A-Letourneau/Projet_Final_TSO/Documentation/Osentreprendre/presentation_mallette_devasion_Louis_Alexis.pdf

# Malette d’évasion

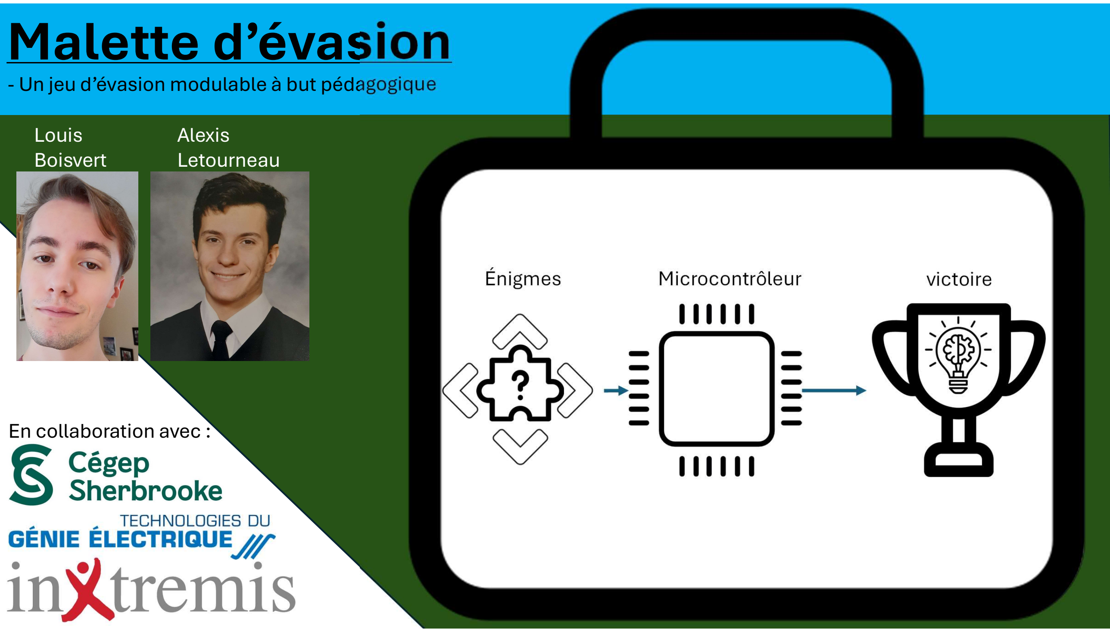
[picture p85: page 1]

Énigmes | Microcontrôleur

Louis
Boisvert

Alexis
Letourneau

victoire

- Un jeu d’évasion modulable à but pédagogique

En collaboration avec :
