A-Letourneau/Projet_Final_TSO/Code/Mallette_GUI/Proto_Fonct_PI/trophy.png

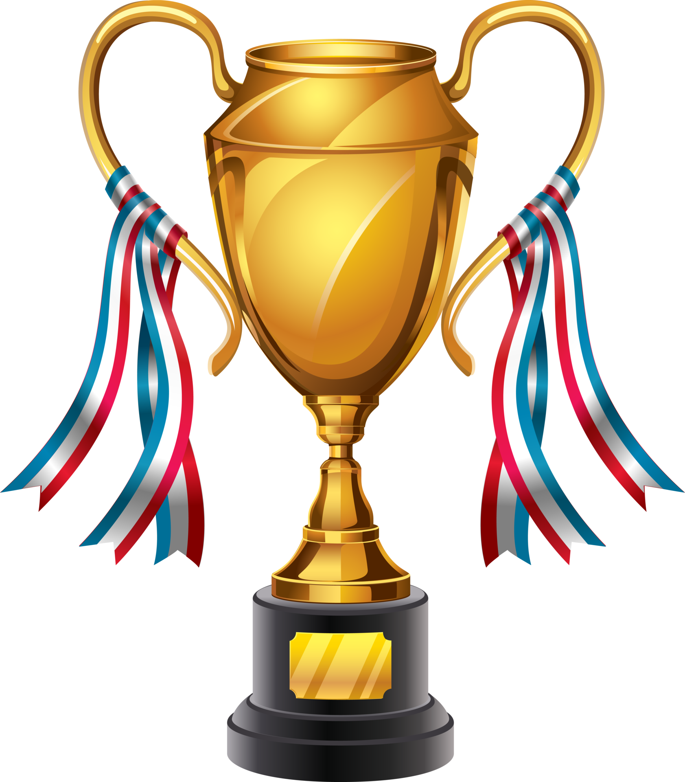
Code/Mallette_GUI/Proto_Fonct_PI/trophy.png
