A-Letourneau/Projet_Final_TSO/Documentation/Manuel_Technique/mallette PIC/20250507_090922.jpg

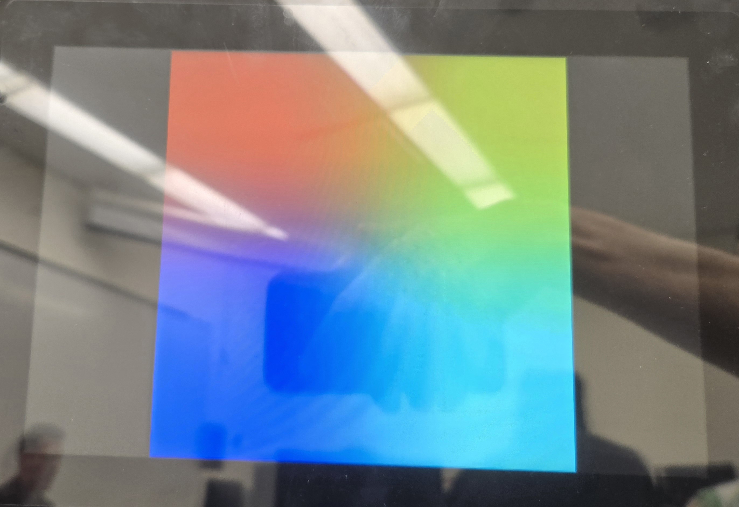
Documentation/Manuel_Technique/mallette PIC/20250507_090922.jpg
