A-Letourneau/Projet_Final_TSO/Documentation/Manuel_Technique/mallette PIC/20250507_091233.jpg

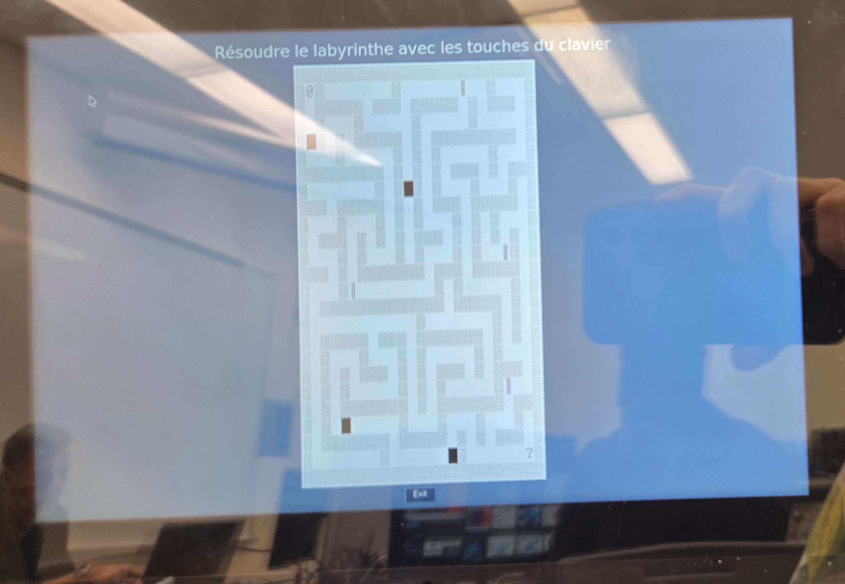
Documentation/Manuel_Technique/mallette PIC/20250507_091233.jpg
