A-Letourneau/Projet_Final_TSO/Documentation/Manuel_Technique/mallette PIC/20250507_091244.jpg

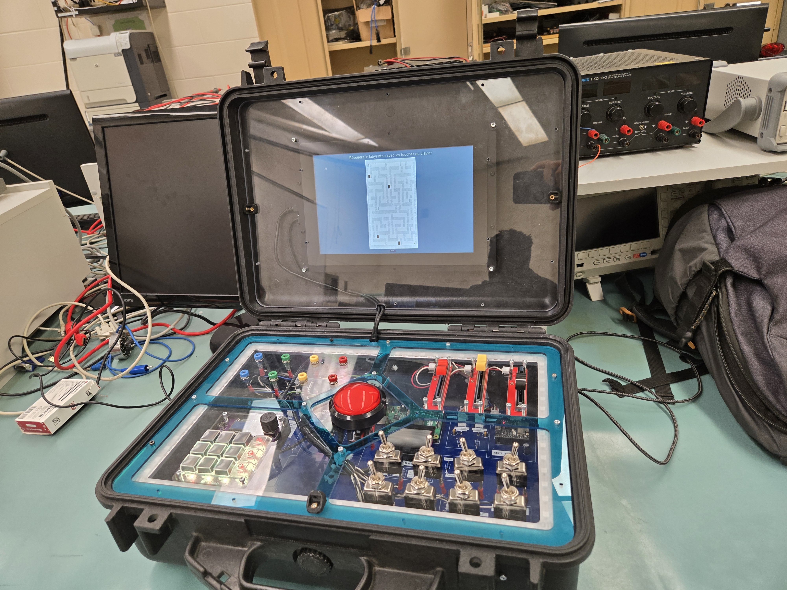
Documentation/Manuel_Technique/mallette PIC/20250507_091244.jpg
