A-Letourneau/Projet_Final_TSO/Matériel/PCB mallette Altium/Raspberry_Pi_4_ModelB.pdf

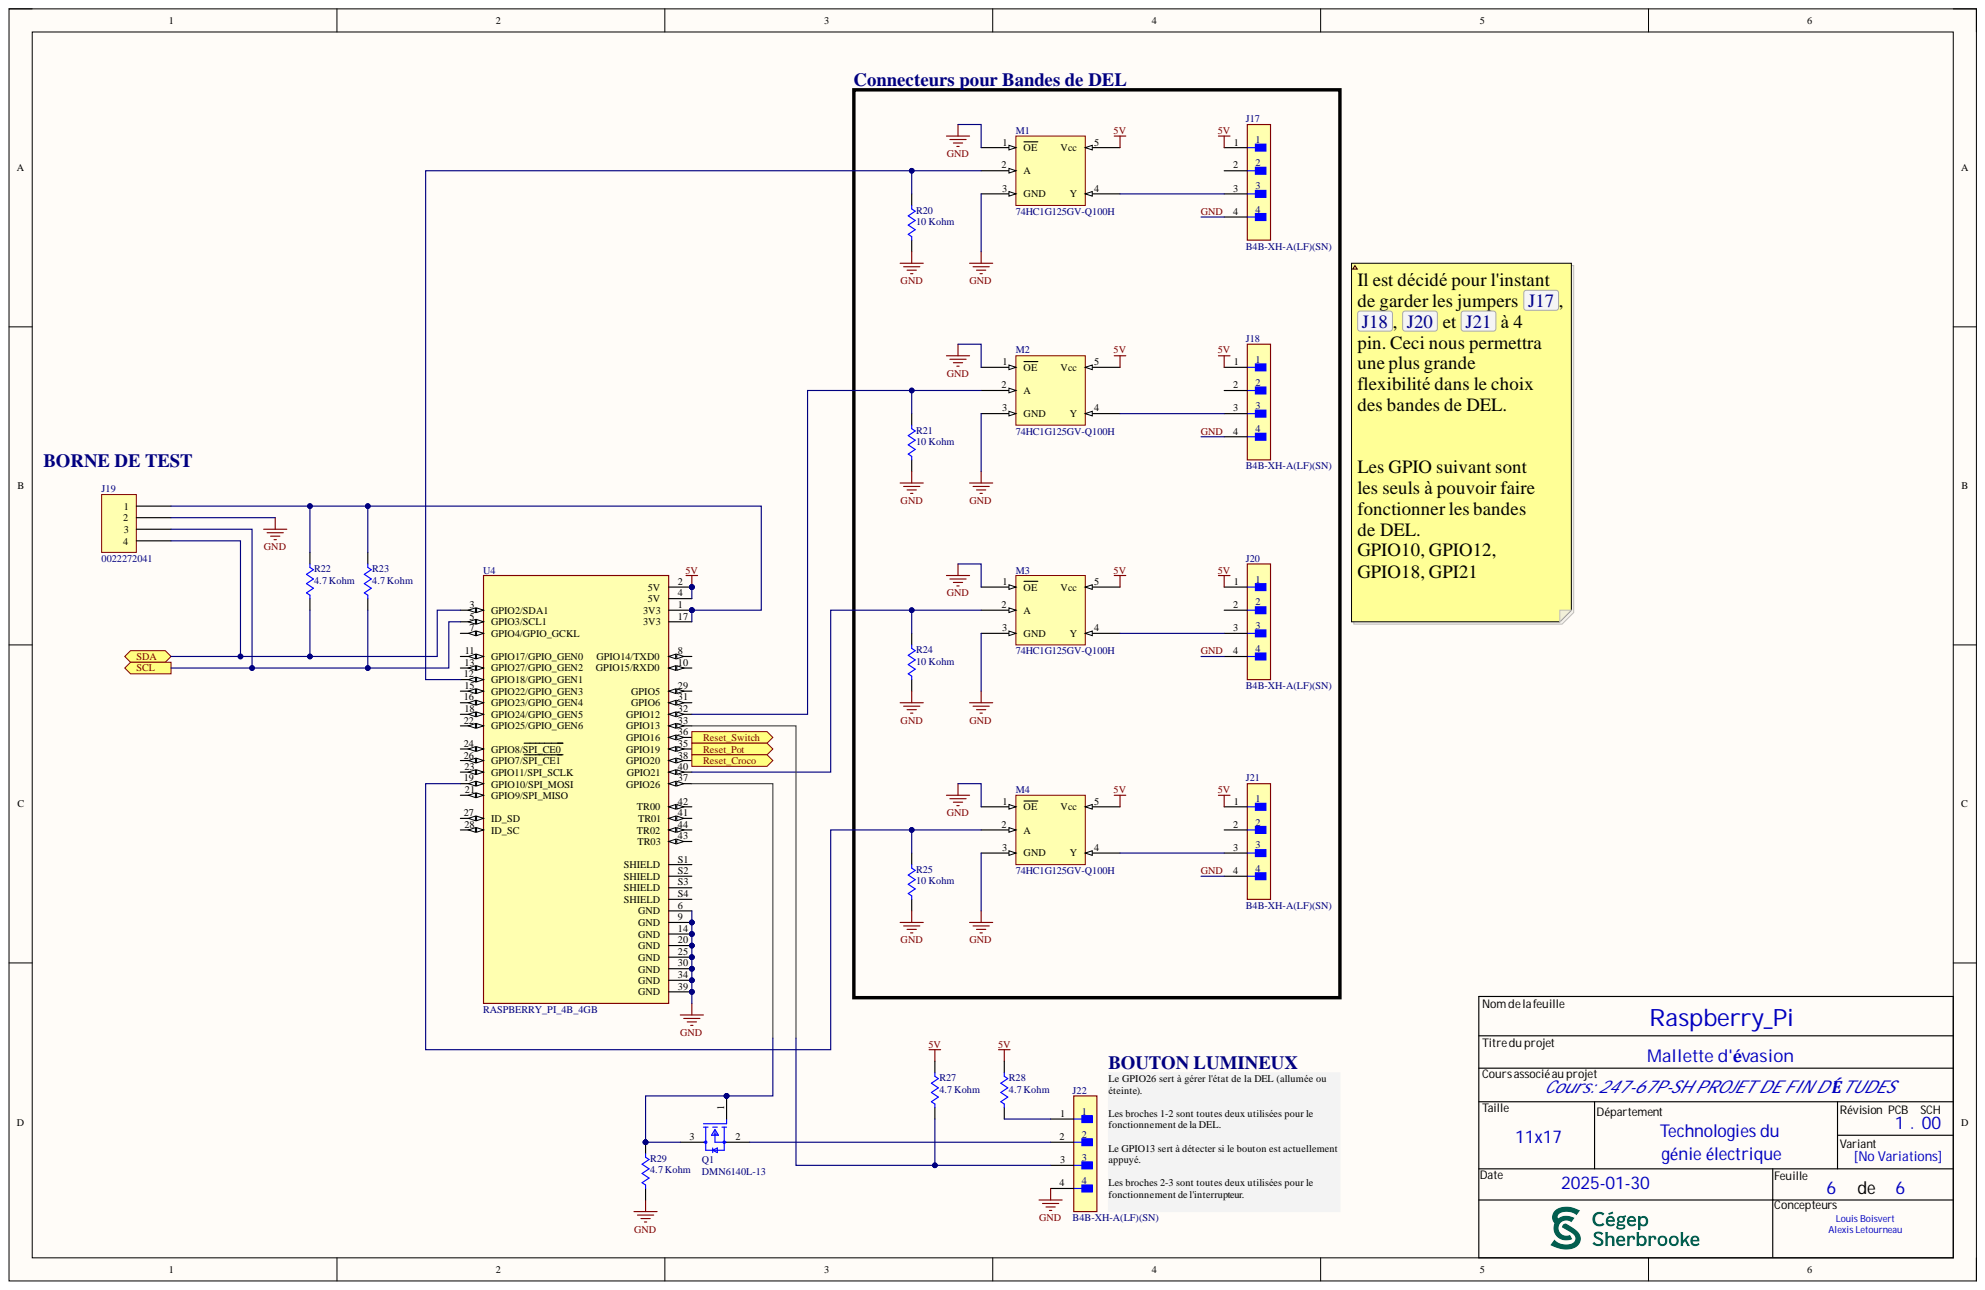
[picture p156: page 1]

Connecteurs pour Bandes de DEL

Il est décidé pour l'instant
de garder les jumpers J17 ,
pin. Ceci nous permettra
une plus grande
flexibilité dans le choix
des bandes de DEL.

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

Nom de la feuille

Titredu projet
Mallette d'évasion Cours associé au projet

Le GPIO26 sert à gérer l'état de la DEL (allumée ou
éteinte).

Cours: 247-67P-SH PROJET DE FIN D'ÉTUDES

Les broches 1-2 sont toutes deux utilisées pour le
fonctionnement de la DEL.

Le GPIO13 sert à détecter si le bouton est actuellement
appuyé.

Les broches 2-3 sont toutes deux utilisées pour le
fonctionnement de l'interrupteur.
