A-Letourneau/Projet_Final_TSO/Code/Mallette_GUI/Proto_Fonct_PI/main.py

#!/home/beaulibe/monenv/bin/python3
"""
Auteur : Alexis Létourneau
Date : 2024-12-03
Environnement : Python, Thonny, raspberry pi 4, ESP32-C3-WROOM-02 Devkit, 
Brief : Programme qui affiche les données reçu par la communication i2c de 3 esp32 externes en mode Sub et qui affiche leurs donnees avec interface PySimpleGUI.
Ce programme communique en i2c en mode Main avec les 3 esp32 en mode Sub. 
Les 3 esp32 ont des objets interactifs (potentiomètres, boutons, interrupteurs) différents, 
Celui nommé SW contient quatre boutons
Celui nommé POT contient 3 potentiomètres et 2 interrupteurs.
Celui nomme Croco est 8 entrees qui transmet si deux des entrees sont interconnecte.
Les lectures de ces objets sont transmises par JSON à la demande du Main à toutes les 50ms


Les 3 esp32 ont une interface chaque, qui contient des "widget" qui représentent leurs états.
L'interface POT utilise deux images d'interrupteurs pointant vers la gauche ou la droite fait en base64, ce qui permet d'avoir le fichier de l'image dans le fichier py directement. 
et utilise des "ProgressBar" pour montrer l'état des potentiomètres.
L'interface SW utilise des images d'interrupteurs pour démontrer l'état des interrupteurs.
L'interface Croco utilise des cercles de couleurs pour montrer qu'elle entrees du esp32 est interconnectee.
Quand on ferme une des fenêtres, les deux se ferme.

"""
#importation des library standard
from smbus2 import SMBus, i2c_msg   #Pour la communication i2c
import PySimpleGUI as sg            #Pour l'interface graphique
import board
from digitalio import DigitalInOut, Direction, Pull
import time
from rpi_ws281x import PixelStrip, Color

#importation des library créer
import moduleDEL    #import Del library obsolète, car elle cause des erreurs lorsqu'il y a plusieurs bandes de dels adressables
from Class_Croco import Croco
import I2c_Comm
from Class_SW import SW_MODULE
from Class_POT import POT
from mazeModule import mazeClass
from button import BTN_CLASS

#Les deux images d'interrupteurs en base 64
TOGGLE_SW_OFF = b'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'
TOGGLE_SW_ON = b'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'

#Les addresses des Sub
SLAVE_ADDRESS_Croco = 0x0b
SLAVE_ADDRESS_SW = 0x0a
SLAVE_ADDRESS_POT = 0x09

#La valeur de refresh en ms
REFRESH_RATE = 50

#Pour les print
DEBUG = False
DEL_ACTIVE = True

# The number of NeoPixels
num_pixels = 100

# luminosités des bandes de dels
lumin = 50

# Pin number
pinStrip1 = 21
#pinStrip2 = 13
pinStrip3 = 12
pinStrip4 = 18 

# Pour les equations
LIST_OPERATIVE = ["+","-","x","/"] #exemple de quatre questions possibles
# LED setup.
led = DigitalInOut(board.D26)
led.direction = Direction.OUTPUT
#BTN setup
switch = DigitalInOut(board.D13)
switch.direction = Direction.INPUT

#Reset setup
resetCroco = DigitalInOut(board.D16)
resetCroco.direction = Direction.OUTPUT

resetSwitch = DigitalInOut(board.D20)
resetSwitch.direction = Direction.OUTPUT

resetPot = DigitalInOut(board.D19)
resetPot.direction = Direction.OUTPUT


#Reset des esp32 pour init la communication
resetCroco.value = False
resetSwitch.value = False
resetPot.value = False
time.sleep(0.01)
resetCroco.value = True
resetSwitch.value = True
resetPot.value = True

def make_winSelect():
    layout_winSelect = [
            [sg.Text("Veuillez selectionner l'enigme desire", size=(35,1), key = "titleSW")],
            [sg.Button("SW"), sg.Button("POT"), sg.Button("Croco")],
            [sg.Button("Labyrinthe"), sg.Button("Bouton")],
            [sg.Button('Exit')]
         ]
    return sg.Window('Fenetre de selection', layout_winSelect, default_element_size=(12, 1) , auto_size_text=False, finalize=True) 

sg.theme("SandyBeach")
#ouvre le menu principal
window_winSelect = make_winSelect()
#window_winSelect.maximize()

#-------------------------------------fonction pour la library Del-------------------------------------#

#fait des objets pour modifier les dels.    (le num de la pin, le nombre de dels, luminosité si c'est GPIO13 ou 19)
strip1 = moduleDEL.initStrip(pinStrip1, num_pixels, lumin, False)
#strip2 = moduleDEL.initStrip(pinStrip2, num_pixels, lumin, True)
strip3 = moduleDEL.initStrip(pinStrip3, num_pixels, lumin, False)
strip4 = moduleDEL.initStrip(pinStrip4, num_pixels, lumin, False)

if DEL_ACTIVE:
    #active les objets strip pour qu'ils puissent être utilisés
    strip1.begin()
#    strip2.begin()
    strip3.begin()
    strip4.begin()


#fait des objets de classes des énigmes
my_Croco = Croco(SLAVE_ADDRESS_Croco, LIST_OPERATIVE, DEBUG, strip1)
my_SW = SW_MODULE(SLAVE_ADDRESS_SW,DEBUG)
mazeEnigme = mazeClass(mazeFile=open(f"/home/beaulibe/Desktop/Mallette_GUI/Proto_Fonct_PI/maze1.txt"), nbGate=4, SLAVE_ADDRESS_MAZE=SLAVE_ADDRESS_SW, DEBUG=DEBUG, DEL_ACTIVE=DEL_ACTIVE)
my_POT = POT(SLAVE_ADDRESS_POT,DEBUG, strip3)
buttonEnigme = BTN_CLASS(switch, led, DEBUG)


if DEL_ACTIVE:
#     moduleDEL.colorWipe(strip1, Color(255, 0, 0), 0)  # Red wipe
#     moduleDEL.colorWipe(strip2, Color(0, 255, 0), 0)  # Red wipe
#     moduleDEL.colorWipe(strip3, Color(0, 0, 255), 0)  # Red wipe
#     moduleDEL.colorWipe(strip4, Color(255, 255, 255), 0)  # Red wipe
    moduleDEL.colorInBetween(strip1, Color(255, 0, 0),0,17)  # Red wipe
    moduleDEL.colorInBetween(strip1, Color(0, 255, 0),18,35)  # Red wipe
    moduleDEL.colorInBetween(strip1, Color(0, 0, 255),36,53)  # Red wipe
    moduleDEL.colorInBetween(strip1, Color(255, 0, 255),54,71)  # Red wipe
    
    moduleDEL.rainbow(strip1,1)

#Boucle principale
while True: 

    if switch.value:
        led.value = False
        if DEBUG:
            print('BTN off')
    else:
        led.value = True
        if DEL_ACTIVE:
            moduleDEL.rainbowCycle(strip4, 0, 1)
        if DEBUG:
            print('BTN on')
        
        
    #-------------Lecture des boutons des fenetres--------------#
    window, event, value = sg.read_all_windows(timeout = REFRESH_RATE)
    
    if window == sg.WIN_CLOSED and event != sg.TIMEOUT_EVENT:
        break
    if event == 'Exit' or event == sg.WIN_CLOSED: #Si on ferme une fenetre on ferme toutes les fenetres
        window.close()
         
        if window == my_SW.window_SW:
            my_SW.window_SW = None
            
        elif window == my_POT.window_POT:
            my_POT.window_POT = None
            
        elif window == my_Croco.window_Croco:
            my_Croco.window_Croco = None
            
        elif window == mazeEnigme.window_maze:
            mazeEnigme.window_maze = None

        elif window == buttonEnigme.window:
            buttonEnigme.window = None
            
        elif window == window_winSelect:
            break
        
    # crée les interfaces utilisateurs selon le choix de l'utilisateurs 
    if event == "SW":
        if not my_SW.window_SW:
            my_SW.window_SW = my_SW.Make_WinSW()
            my_SW.window_SW.maximize()
            
    if event == "POT":
        if not my_POT.window_POT:
            my_POT.window_POT = my_POT.Make_WinPOT()
            my_POT.window_POT.maximize()
    
    if event == "Croco":
        if not my_Croco.window_Croco:
            my_Croco.window_Croco = my_Croco.Make_WinCroco()
            my_Croco.window_Croco.maximize()
            
    if event == "Bouton":
        if not buttonEnigme.window:
            buttonEnigme.window = buttonEnigme.Make_WinBTN()
#            buttonEnigme.window.maximize()        
            
    if event == "Labyrinthe":
        if not mazeEnigme.window_maze:
            mazeEnigme.startMaze()
            mazeEnigme.window_maze.maximize()
            
    #Essaye de lire les json des esp32 et met un message d'erreur s'il n'y parvient pas
    if my_Croco.window_Croco:
        my_Croco.msg_Croco = my_Croco.Croco_Json()
        my_Croco.doWinCroco()
        
    if my_SW.window_SW: 
        my_SW.msg_SW = my_SW.SW_Json()
        
    if  my_POT.window_POT:    
        my_POT.msg_POT = my_POT.POT_Json()
        my_POT.doWinPot()
    
    if mazeEnigme.window_maze:
        mazeEnigme.doMaze()
        
    if buttonEnigme.window:
        buttonEnigme.doButton()
    
    #débute les énigmes si leur fenêtre est présentement ouverte
    # et va changer les couleurs des strips de dels lorsque l'utilisateur va réussir
    

#À la fin du programme, on ferme les fenêtres s'il existe
if my_SW.window_SW:
    my_SW.window_SW.close()       
if my_POT.window_POT:    
    my_POT.window_POT.close()            
if my_Croco.window_Croco: 
    my_Croco.window_Croco.close()

print("closing")
