A-Letourneau/Projet_Final_TSO/Code/Mallette_GUI/Code de test/dinosaur.py

import PySimpleGUI as sg

"""
    Demo_Animated_GIFs.py
    
    Shows how to:
    * Use popup_animated
    * Use animated GIF in a custom window layout
    * Store your GIFs in base64 format inside this source file (copy and paste into your source file)
    
    The first image that uses popup_animated will stop after a few seconds on its own.
    The remaining images are shown 1 at a time. To move on to the next image, click the current image.
    If you want to exit before reaching the final image, right click the image and choose 'exit'
"""

# ---------------------------- Base 64 GIFs ----------------------------
gif = b'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'

# list of all of the base64 GIFs
# first show how to use popup_animated using built-in GIF image
for i in range(1000):
    sg.popup_animated(sg.DEFAULT_BASE64_LOADING_GIF, background_color='white', time_between_frames=100)
sg.popup_animated(None)      # close all Animated Popups


# Next demo is to show how to create custom windows with animations
layout = [[sg.Image(data=gif, enable_events=True, background_color='white', key='-IMAGE-', right_click_menu=['UNUSED', 'Exit'])],]

window = sg.Window('My new window', layout,
        grab_anywhere=True,
        keep_on_top=True,
        background_color='white',
        transparent_color='white',
        alpha_channel=.8,
        margins=(0,0))



while True:                                     # Event Loop
    event, values = window.read(timeout=10)     # loop every 10 ms to show that the 100 ms value below is used for animation
    if event in (None, 'Exit', 'Cancel'):
        break
    window['-IMAGE-'].update_animation(gif,  time_between_frames=100)
