A-Letourneau/Projet_Final_TSO/Code/Mallette_GUI/Proto_Fonct_PI/Class_Croco.py

"""
Auteur : Louis Boisvert & Alexis Létourneau
Date : 2025-03-11
Environnement : Python, Thonny, raspberry pi 4, ESP32-C3-WROOM-02 Devkit, 
Brief : Cette Class représentes l'énigmes des fils bananes que l'on a renommé à Croco
par simplicité.

- la fonction "Croco_Json" appel le fichier I2c_Comm ce qui permet de récupérer
les informations du esp32 servant à l'énigme Croco
- la fonction "Make_WinCroco" crée l'interface utilisateur
- la fonction "Start_WinCroco" est la portion de code qui va gérer l'énigme grâce au
information récupérer par "Croco_Json".

Commentaire : la vérification de la réussite des utilisateur pourrait être dans
sa propre fonction
(Louis)

"""

#importation des library standard
from smbus2 import SMBus, i2c_msg   #Pour la communication i2c
import PySimpleGUI as sg            #Pour l'interface graphique
import json                         #Pour la manipulation des json
from random import randint          #Pour la generation de nombre aleatoire pour les equations
# library pour les strips de dels
import time
from rpi_ws281x import PixelStrip, Color

#importation des library créer
import I2c_Comm
import moduleDEL


class Croco:
    
    #------------------- les variables statiques utilisés par l'énigme des fils bananes -------------------#
    #Nombre d'entrées Croco
    NB_CROCO = 8
    #Couleur des paires de Croco
    listColor = ["red","pink","yellow","cyan"]
    
    
    #------------------- les varibles qui dépendent du 'main.py' ou/et qui sont utilisés dans plus d'une fonction -------------------#
    def __init__(self, SLAVE_ADDRESS_Croco, LIST_OPERATIVE, DEBUG, strip, REPEAT_PUZZLE = True):
        #Liste les operations des question en ordre
        self.LIST_OPERATIVE = LIST_OPERATIVE      
        self.SLAVE_ADDRESS_Croco = SLAVE_ADDRESS_Croco
        self.DEBUG = DEBUG
        self.Crocoerror = False
        self.window_Croco = None
        self.strip = strip
        self.REPEAT_PUZZLE = REPEAT_PUZZLE
        self.puzzleSolved = False
        #Initiation du jeu d'equation
        self.firstEquation = True
        self.randomAnswer = 0 #La reponse aleatoire
        self.goodAnswer = 0 #Nombre de bonnes reponses
        
        self.minDEL = 54
        self.maxDEL = 71
        
    def resetPuzzle(self):
        self.Crocoerror = False
        self.puzzleSolved = False
        #Initiation du jeu d'equation
        self.firstEquation = True
        self.randomAnswer = 0 #La reponse aleatoire
        self.goodAnswer = 0 #Nombre de bonnes reponses

    #Crée un graph pour contenir un rond de couleur
    def DrawRGB(self, key=None, radius=150):
        return sg.Graph(canvas_size=(radius, radius),
                 graph_bottom_left=(-radius, -radius),
                 graph_top_right=(radius, radius),
                 pad=(0, 0), key=key)


    #Efface puis crée un rond de couleur pour représenter l'état des boutons
    def SetRGB(self, window, key, color):
        graph = window[key]
        graph.erase()
        graph.draw_circle((0, 0), 100 , fill_color=color, line_color=color)
        graph.draw_text( str((int(key) + 1)) , (0, 0), font=14)
     
     
    #essaie la communication I2c et la reception des donnees (louis)
    def Croco_Json(self):
        global Crocoerror
        self.msg_Croco = ""
        if self.window_Croco: 
            try:
                self.msg_Croco = I2c_Comm.sendRequest(self.SLAVE_ADDRESS_Croco, self.DEBUG)
                Crocoerror = False
                self.window_Croco["titleCroco"].update(text_color = None)
            except:
                self.window_Croco["titleCroco"].update(text_color = "red")
                Crocoerror = True
                if self.DEBUG:
                    print("Croco i2c ERROR")
        return self.msg_Croco
   
   
    #crée l'interface utilisateur pour l'énigme Croco 
    def Make_WinCroco(self):
        layout_Croco =[
                    [sg.VPush()],
                    [sg.Push(), sg.Text("",  key = "countDown", size=(17,1), font='Algerian 15', justification = "center"), sg.Push()],
                    [sg.Push(), sg.Text(f"Nombre d'équation restante 0/{len(self.LIST_OPERATIVE)}", size=(40,1), key = 'titleCroco', font='Algerian 20', justification = "center"), sg.Push()],
                    [sg.Push(), sg.Text("Veuillez connecter les bornes bananes\navec le fil pour compléter l'équation", size=(40,2), key = 'titleCroco', font='Algerian 20', justification = "center"), sg.Push()],
                    [sg.Push(), sg.Text("", size=(10,1), key="equation", font='Algerian 50', justification = "center", ), sg.Push()],
                    [sg.Push(), self.DrawRGB('0'), self.DrawRGB('1'), self.DrawRGB('2'), self.DrawRGB('3'), sg.Push()],
                    [sg.Push(), self.DrawRGB('4'), self.DrawRGB('5'), self.DrawRGB('6'), self.DrawRGB('7'), sg.Push()],          
                    [sg.VPush()]
                  ]
        return sg.Window('Fenêtre énigme equation', layout_Croco, default_element_size=(12, 1), auto_size_text=False, finalize=True, keep_on_top=True)


    #cette fonction est le coeur de l'énigme. c'est ici que l'utilisateur va pouvoir essayer de résoudre l'énigme.
    def doWinCroco(self):
        global Crocoerror
       #-----------Fenêtre Interface Croco-----------#
        if self.window_Croco and not Crocoerror: #Detecte si la fenetre existe puis detecte si le i2c fonctionne. L'ordre est important car si la fenetre est None, le Crocoerror n'existe pas
            curCroco = 0 #La paire de Croco actuel
            colorCpt = 0 #la couleur de paire actuel
            dictOfPairsColor = {} #Pour mettre la couleur en memoire pour la deuxieme fois qu'on voit la paire
            answer = 0 #Reponse de l'usager
            firstNum = 0
            secondNum = 0
            
            #Pour chaque connection du Json, on met un rond de couleur pour l'associer avec sa paire
            for pairs in self.msg_Croco['JsonData']:
                if int(pairs) == self.NB_CROCO: #Le 8 signifit qu'il n'y pas de connection
                    self.SetRGB(self.window_Croco, str(curCroco), 'white')
                elif curCroco < int(pairs): #Si c'est la premiere fois qu'on voit cette paire
                    self.SetRGB(self.window_Croco, str(curCroco), self.listColor[colorCpt]) #On met le rond de couleur a la position curCroco en une des 4 couleurs possible en ordre
                    dictOfPairsColor[str(curCroco)] = self.listColor[colorCpt]#On met la couleur en memoire pour la deuxieme fois qu'on voit la paire
                    colorCpt = colorCpt + 1 #On passe a la prochaine couleur
                    
                    if self.LIST_OPERATIVE[self.goodAnswer] == "+": #Fait la bonne operation selon l'operation, mais additionne toujours les paires
                        firstNum  = (int(pairs) + 1)
                        secondNum = (curCroco + 1)
                        answer += (curCroco + 1) + (int(pairs) + 1)
                    elif self.LIST_OPERATIVE[self.goodAnswer] == "-":
                        firstNum  = (int(pairs) + 1)
                        secondNum = (curCroco + 1)
                        answer += (int(pairs) + 1) - (curCroco + 1)
                    elif self.LIST_OPERATIVE[self.goodAnswer] == "x":
                        firstNum  = (int(pairs) + 1)
                        secondNum = (curCroco + 1)
                        answer += (curCroco + 1) * (int(pairs) + 1)
                    elif self.LIST_OPERATIVE[self.goodAnswer] == "/":
                        firstNum  = (int(pairs) + 1)
                        secondNum = (curCroco + 1)
                        answer += (int(pairs) + 1) / (curCroco + 1)
                    
                else:  #Si c'est la deuxieme fois qu'on voit cette paire
                    try: #
                        self.SetRGB(self.window_Croco, str(curCroco), dictOfPairsColor[pairs])
                    except:
                        if self.DEBUG:
                            self.SetRGB(self.window_Croco, str(curCroco), "red")
                            
                curCroco = curCroco + 1
            if firstNum == 0 and secondNum == 0:
                firstNum = "?"
                secondNum = "?"
            if self.LIST_OPERATIVE[self.goodAnswer] != '/':
                self.window_Croco["equation"].update(f"{self.randomAnswer}={firstNum}{self.LIST_OPERATIVE[self.goodAnswer]}{secondNum}")
            else:
                self.window_Croco["equation"].update(f"{self.randomAnswer:.3f}={firstNum}{self.LIST_OPERATIVE[self.goodAnswer]}{secondNum}")
                                  
                
            if self.firstEquation or answer == self.randomAnswer: 
                if not self.firstEquation:
                    self.goodAnswer += 1

                    self.window_Croco["titleCroco"].update(f"Nombre d'équation restante {self.goodAnswer}/{len(self.LIST_OPERATIVE)}")
                    #On met les bonnes connections a vert
                    curCroco = 0
                    for pairs in self.msg_Croco['JsonData']:
                        if int(pairs) == self.NB_CROCO: #Le 8 signifit qu'il n'y pas de connection
                            self.SetRGB(self.window_Croco, str(curCroco), 'white')
                        else: #Si c'est la premiere fois qu'on voit cette paire
                            self.SetRGB(self.window_Croco, str(curCroco), 'green') #On met le rond de couleur a la position curCroco en une des 4 couleurs possible en ordre
                        curCroco = curCroco + 1
                    self.window_Croco.read(timeout=0)
                    time.sleep(2)
                else:
                    self.firstEquation = False

                if self.goodAnswer == len(self.LIST_OPERATIVE): #Lorsque l'user a finit les questions
                    moduleDEL.colorInBetween(self.strip, Color(0, 255, 0), self.minDEL, self.maxDEL)  # Red wipe
                    if self.REPEAT_PUZZLE:
                        self.goodAnswer = 0
                        self.firstEquation = True
                        self.window_Croco["titleCroco"].update(f"Nombre d'équation restante {self.goodAnswer}/{len(self.LIST_OPERATIVE)}")
                    else:
                        self.puzzleSolved = True
                        sg.popup_auto_close('Énigme réussi!!', auto_close_duration=3, font='Algerian 20')
                        
                    
                #Tout les reponses aleatoires doivent etre different de l'ancien pour ne pas resoudre immediatement
                elif self.LIST_OPERATIVE[self.goodAnswer] == "+":
                    while True:
                        newRandomAnswer = randint(3,15)
                        if newRandomAnswer != self.randomAnswer:
                            self.randomAnswer = newRandomAnswer
                            break
                        
                elif self.LIST_OPERATIVE[self.goodAnswer] == "-":
                    while True:
                        newRandomAnswer = randint(1,7)
                        if newRandomAnswer != self.randomAnswer:
                            self.randomAnswer = newRandomAnswer
                            break
                        
                elif self.LIST_OPERATIVE[self.goodAnswer] == "x":
                    while True:
                        newRandomAnswer = randint(1,8)
                        newRandomAnswer2 = randint(1,8)
                        if self.randomAnswer != newRandomAnswer * newRandomAnswer2 and newRandomAnswer != newRandomAnswer2: #Un nombre qui n'est pas carre
                            self.randomAnswer = newRandomAnswer * newRandomAnswer2
                            break
                        
                elif self.LIST_OPERATIVE[self.goodAnswer] == "/":
                    while True:
                        newRandomAnswer = randint(2,8)
                        newRandomAnswer2 = randint(2,8)
                        if newRandomAnswer2 < newRandomAnswer and self.randomAnswer != newRandomAnswer * newRandomAnswer2 and newRandomAnswer != newRandomAnswer2: #Un nombre qui n'est pas 1 et pas plus petit que zero
                            self.randomAnswer = newRandomAnswer / newRandomAnswer2
                            break
