A-Letourneau/Projet_Final_TSO/Code/Mallette_GUI/Code de test/Minesweeper.py

import PySimpleGUI as sg
import random
import sys

'''
The classic Minesweeper game
Original code was posted here:
https://pysimplegui.trinket.io/sites/minesweeper

Requires PySimpleGUI version 4.11.0 and higher
''' 

blank = b'iVBORw0KGgoAAAANSUhEUgAAAB4AAAAeCAYAAAA7MK6iAAAAAXNSR0IArs4c6QAAAARnQU1BAACxjwv8YQUAAAAJcEhZcwAAEnQAABJ0Ad5mH3gAAAA5SURBVEhL7c0xAQAgDMTABynVU7MohAUN6ZJbMmbV6ZsB+xfnGOMY4xjjGOMY4xjjGOMY4xgzNE4euGMCWklhg+IAAAAASUVORK5CYII='
bomb = b'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'
flag = b'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'

# On Windows runs best with board size of 20 x 14 and bombs = 80
font        = 'Courier 16 bold'
width       = 10    # Board Width
height      = 8     # Board Height
all         = 10    # BOMBS
new_start   = True
size        = (30,30)
# 0: 0, 1: hidden card, 2: bomb card, 3: flag card, 4: shown card
im          = ['', blank, bomb,flag, '']
color       = [('grey', 'grey'), ('black', 'green'),
               ('black', 'green'), ('black', 'green'), ('black', 'grey')]

def binding_all():                  # Bind right button of mouse to cell object

    for x in range(width):
        for y in range(height):
            window[b[x][y].key].bind(
                '<Button-3>', '+RIGHT')

# Setting for top buttons
def button1(text, key=None, disabled=False, button_color=('white', 'green')):

    return sg.Button(text, pad=(10, 10), font=font, focus=False, key=key,
            disabled=disabled, button_color=button_color)

def button2(x, y):                  # define cell as instance of button and

    b[x][y] = button(x,y)           # bulid Button
    return b[x][y].button

def check_blank(x, y):              # Check if cell near 0-bomb cel

    if b[x][y].num==0: return False
    for i in [-1, 0, 1]:
        for j in [-1, 0, 1]:
            if i==0 and j==0: continue
            if ((0<=x+i<width) and (0<=y+j<height) and
                (b[x+i][y+j].num==0)): return True
    return False

def check_num():                    # check number of bombs, flags and hides

    bomb_count = flag_count = hide_count = 0
    for x in range(width):
        for y in range(height):
            if b[x][y].state == 1:
                hide_count += 1
            elif b[x][y].state == 2:
                bomb_count += 1
            elif b[x][y].state == 3:
                flag_count += 1
    return bomb_count, flag_count, hide_count

# Count number of bombs about cell
def count_bomb(x, y):

    global bomb
    if bomb[x][y]==10: return 10
    count = 0
    for i in [-1, 0, 1]:
        for j in [-1, 0, 1]:
            if i==0 and j==0: continue
            if ((0<=x+i<width) and (0<=y+j<height) and
                (bomb[x+i][y+j]==10)):
                count += 1
    return count

# set position for all boms
def deal():

    global bomb
    bomb_list   = random.sample(range(width*height), all)
    bomb        = [[0 for y in range(height)] for x in range(width)]

    for x in range(width):
        for y in range(height):
            if x*height+y in bomb_list: bomb[x][y]=10

    for x in range(width):
        for y in range(height):
            bomb[x][y] = count_bomb(x, y)

    return

def new_card():                     # refresh all cells to hidden card

    for x in range(width):
        for y in range(height):
            b[x][y].state = 1
            b[x][y].num = bomb[x][y]
            b[x][y].color = color[1]
            b[x][y].update(1)

def show_blank():                   # Show all cell not around by any bomb

    for x in range(width):
        for y in range(height):
            if b[x][y].num == 0:
                b[x][y].update(0)
            elif check_blank(x, y):
                b[x][y].update(4)

# Class for each button object
class button():

    def __init__(self, x, y):

        self.x          = x
        self.y          = y
        self.state      = 1
        self.color      = color[self.state]
        self.disabled   = False
        self.key        = (x,y)             # keys can be ANYTHING, not just strings
        self.num        = bomb[x][y]
        self.button     = sg.Button(' ',
            auto_size_button=False,
            border_width=2,
            button_color=self.color,
            disabled=self.disabled,
            focus=False,
            font=font,
            image_size=size,
            # image_filename=im[self.state],
            image_data=im[self.state],
            key=self.key,
            pad=(1,1))

    def right_click(self):   # Right_click handler

        if self.state == 1:
            self.update(3)
        elif self.state == 3:
            self.update(1)

    def update(self, state):        # update state of cell

        self.state = state
        if state == 0:
            self.disabled = True
            text = ' '
        elif state in [1,2,3]:
            self.disabled = False
            text = ' '
        elif state == 4:
            self.disabled = True
            text = str(self.num)
        self.color = color[self.state]
        window[self.key].Widget['disabledforeground'] = 'white'
        self.button.Update(text=text, disabled=self.disabled,
            # image_filename=im[self.state],
            image_data=im[self.state],
            image_size=size,
            button_color=self.color)


def startGame():

    sg.change_look_and_feel('DarkGreen')

    deal()  # Initial position of bombs
    global b
    b = [[0 for j in range(height)] for i in range(width)]

    layout  = [[button1('New Game', key='-New Game-'),  # Layout of window
                button1('Game Over', key='-Game Over-'),
                button1('Target:'+str(all), key='-Target-'),
                button1('Bomb:0', key='-Count-Bomb-'),
                button1('Flag:0', key='-Count-Flag-')]]+[
                [button2(x, y) for x in range(width)] for y in range(height)]
    global window
    window = sg.Window('MineSweeper', layout=layout, finalize=True, keep_on_top=True) # Create window


    binding_all()       # Binding right button event handler of all cells
    show_blank()        # Show all cells near no-bomb cell

    new_start   = True  # Flag for new game
    message     = False # Flag for game over message sent



    while True:

        if new_start:   # Actions for new game

            deal()
            new_card()
            show_blank()
            message = False
            new_start = False
            pass

        event, values = window.read()    # read window event

        if event==None or event=='-Game Over-':     # Window close / Game over
            break

        elif event == '-New Game-':                 # New Game, set the flag
            new_start = True

        elif isinstance(event, tuple):              # buttons have tuple for event
            right_click = False
            if isinstance(event[0], tuple):         # if the tuple has a tuple, then it's a right click event
                x,y = event[0]
                right_click = True
            else:
                x, y = event
            if not right_click:
                if b[x][y].state == 1:
                    if b[x][y].num == 10:
                        b[x][y].update(2)
                    else:
                        b[x][y].update(4)
            else:
                b[x][y].right_click()
        # Update number onf bombs, flags
        bomb_num, flag_num, hide_num = check_num()
        window['-Count-Bomb-'].Update(text='Bomb:'+str(bomb_num))
        window['-Count-Flag-'].Update(text='Flag:'+str(flag_num))

        # Check if game over
        if hide_num==0 and (bomb_num+flag_num==all) and (not message):
            message = True
            sg.popup('Game Over', title='Note', keep_on_top=True)
        

    window.close()
